eldar6776/RelayExpander/fw/DE-260124/Core/Src/modbus.c

/**
 ******************************************************************************
 * Project          : RELAY EXPANDER
 ******************************************************************************
 *
 *
 ******************************************************************************
 */

#if (__MODBUS_H__ != FW_BUILD)
    #error "modbus header version mismatch"
#endif 
/* Includes ------------------------------------------------------------------*/
#include "modbus.h"
#include <string.h>
/* Imported Types  -----------------------------------------------------------*/
/* Imported Variables --------------------------------------------------------*/
/* Imported Functions    -----------------------------------------------------*/
/* Private Typedef -----------------------------------------------------------*/
/* Private Define  -----------------------------------------------------------*/
#define COIL_ON     0x01
#define COIL_OFF    0x02
#define COIL_TOGGLE 0x03
#define COIL_READ   0x03
#define COIL_WRITE  0x06
//
/* Private Variables  --------------------------------------------------------*/
static uint8_t rec_buf[256], send_buf[32], rel[4];
static uint8_t  recb, recl, coil_max = 16, addr = 0;
/* Private macros   ----------------------------------------------------------*/
/* Private Function Prototypes -----------------------------------------------*/
static uint8_t chk_crc(uint8_t *buf);
static void mb_send(uint8_t *sb, uint8_t len);
static uint32_t getCRC16_Modbus(const uint8_t *nData, uint32_t wLength);
/* Program Code  -------------------------------------------------------------*/
/**
  * @brief
  * @param
  * @retval
  */
void mb_init(void)
{
    memset(rec_buf,0, sizeof(rec_buf));
    memset(rec_buf, 0, sizeof(rec_buf));
    memset(send_buf, 0, sizeof(send_buf));
    HAL_UART_Receive_IT(&huart1, &recb, 1);
    if(HAL_GPIO_ReadPin(SELECT_0_GPIO_Port, SELECT_0_Pin) == GPIO_PIN_RESET) addr |= 0x01U;
    if(HAL_GPIO_ReadPin(SELECT_1_GPIO_Port, SELECT_1_Pin) == GPIO_PIN_RESET) addr |= 0x02U;
    if(HAL_GPIO_ReadPin(SELECT_2_GPIO_Port, SELECT_2_Pin) == GPIO_PIN_RESET) addr |= 0x04U;
    if(HAL_GPIO_ReadPin(SELECT_3_GPIO_Port, SELECT_3_Pin) == GPIO_PIN_RESET) addr |= 0x08U;
    if(HAL_GPIO_ReadPin(SELECT_4_GPIO_Port, SELECT_4_Pin) == GPIO_PIN_RESET) addr |= 0x10U;
    if(HAL_GPIO_ReadPin(SELECT_16_32_GPIO_Port, SELECT_16_32_Pin) == GPIO_PIN_RESET) coil_max = 32;
}

void mb_service(void)
{
        uint8_t i;
    if(recl >= 8)
    {   
        i = 0;
        while(i < recl)
        {
            if(rec_buf[i] == addr)
            {
                if(rec_buf[i+1] == COIL_READ)
                {
                    if(rec_buf[i+3] < coil_max)
                    {
                        if(chk_crc(&rec_buf[i]))
                        {
                            
                        }
                    }
                }
                else if (rec_buf[i+1] == COIL_WRITE)
                {
                    if(rec_buf[i+3] < coil_max)
                    {
                        if(chk_crc(&rec_buf[i]))
                        {
                            if(rec_buf[i+4] == COIL_ON)
                            {
                                
                            }
                            else if(rec_buf[i+4] == COIL_OFF)
                            {
                                
                            }
                            else if(rec_buf[i+4] == COIL_TOGGLE)
                            {
                                
                            }
                        }
                    }
                }
            }            
            i++;
        }
    }
}


static void mb_send(uint8_t *sb, uint8_t len)
{
    HAL_UART_Transmit(&huart1,(uint8_t*)sb, len, RESP_TOUT);
    HAL_UART_Receive_IT(&huart1, &recb, 1);
}


static uint8_t chk_crc(uint8_t *buf)
{
    uint8_t crc[2];
    *((uint16_t*)crc) = getCRC16_Modbus(buf, 6);
    if((buf[6] == crc[0])&&(buf[7] == crc[1])) return 1;
    return 0;
}

static uint32_t getCRC16_Modbus(const uint8_t *nData, uint32_t wLength)
{
    static const uint32_t wCRCTable[] = 
    {
        0X0000, 0XC0C1, 0XC181, 0X0140, 0XC301, 0X03C0, 0X0280, 0XC241,
        0XC601, 0X06C0, 0X0780, 0XC741, 0X0500, 0XC5C1, 0XC481, 0X0440,
        0XCC01, 0X0CC0, 0X0D80, 0XCD41, 0X0F00, 0XCFC1, 0XCE81, 0X0E40,
        0X0A00, 0XCAC1, 0XCB81, 0X0B40, 0XC901, 0X09C0, 0X0880, 0XC841,
        0XD801, 0X18C0, 0X1980, 0XD941, 0X1B00, 0XDBC1, 0XDA81, 0X1A40,
        0X1E00, 0XDEC1, 0XDF81, 0X1F40, 0XDD01, 0X1DC0, 0X1C80, 0XDC41,
        0X1400, 0XD4C1, 0XD581, 0X1540, 0XD701, 0X17C0, 0X1680, 0XD641,
        0XD201, 0X12C0, 0X1380, 0XD341, 0X1100, 0XD1C1, 0XD081, 0X1040,
        0XF001, 0X30C0, 0X3180, 0XF141, 0X3300, 0XF3C1, 0XF281, 0X3240,
        0X3600, 0XF6C1, 0XF781, 0X3740, 0XF501, 0X35C0, 0X3480, 0XF441,
        0X3C00, 0XFCC1, 0XFD81, 0X3D40, 0XFF01, 0X3FC0, 0X3E80, 0XFE41,
        0XFA01, 0X3AC0, 0X3B80, 0XFB41, 0X3900, 0XF9C1, 0XF881, 0X3840,
        0X2800, 0XE8C1, 0XE981, 0X2940, 0XEB01, 0X2BC0, 0X2A80, 0XEA41,
        0XEE01, 0X2EC0, 0X2F80, 0XEF41, 0X2D00, 0XEDC1, 0XEC81, 0X2C40,
        0XE401, 0X24C0, 0X2580, 0XE541, 0X2700, 0XE7C1, 0XE681, 0X2640,
        0X2200, 0XE2C1, 0XE381, 0X2340, 0XE101, 0X21C0, 0X2080, 0XE041,
        0XA001, 0X60C0, 0X6180, 0XA141, 0X6300, 0XA3C1, 0XA281, 0X6240,
        0X6600, 0XA6C1, 0XA781, 0X6740, 0XA501, 0X65C0, 0X6480, 0XA441,
        0X6C00, 0XACC1, 0XAD81, 0X6D40, 0XAF01, 0X6FC0, 0X6E80, 0XAE41,
        0XAA01, 0X6AC0, 0X6B80, 0XAB41, 0X6900, 0XA9C1, 0XA881, 0X6840,
        0X7800, 0XB8C1, 0XB981, 0X7940, 0XBB01, 0X7BC0, 0X7A80, 0XBA41,
        0XBE01, 0X7EC0, 0X7F80, 0XBF41, 0X7D00, 0XBDC1, 0XBC81, 0X7C40,
        0XB401, 0X74C0, 0X7580, 0XB541, 0X7700, 0XB7C1, 0XB681, 0X7640,
        0X7200, 0XB2C1, 0XB381, 0X7340, 0XB101, 0X71C0, 0X7080, 0XB041,
        0X5000, 0X90C1, 0X9181, 0X5140, 0X9301, 0X53C0, 0X5280, 0X9241,
        0X9601, 0X56C0, 0X5780, 0X9741, 0X5500, 0X95C1, 0X9481, 0X5440,
        0X9C01, 0X5CC0, 0X5D80, 0X9D41, 0X5F00, 0X9FC1, 0X9E81, 0X5E40,
        0X5A00, 0X9AC1, 0X9B81, 0X5B40, 0X9901, 0X59C0, 0X5880, 0X9841,
        0X8801, 0X48C0, 0X4980, 0X8941, 0X4B00, 0X8BC1, 0X8A81, 0X4A40,
        0X4E00, 0X8EC1, 0X8F81, 0X4F40, 0X8D01, 0X4DC0, 0X4C80, 0X8C41,
        0X4400, 0X84C1, 0X8581, 0X4540, 0X8701, 0X47C0, 0X4680, 0X8641,
        0X8201, 0X42C0, 0X4380, 0X8341, 0X4100, 0X81C1, 0X8081, 0X4040 
    };

    uint8_t nTemp;
    uint32_t wCRCWord = 0xFFFF;

    while (wLength--)
    {
        nTemp = *nData++ ^ wCRCWord;
        wCRCWord >>= 8;
        wCRCWord ^= wCRCTable[nTemp];
    }
    return wCRCWord;
}

void HAL_UART_RxCpltCallback(UART_HandleTypeDef *huart){
    rec_buf[recl++] = recb;
    HAL_UART_Receive_IT(&huart1, &recb, 1);
}
/**
  * @brief
  * @param
  * @retval
  */
void HAL_UART_TxCpltCallback(UART_HandleTypeDef *huart){
}
/**
  * @brief
  * @param
  * @retval
  */
void HAL_UART_ErrorCallback(UART_HandleTypeDef *huart){
    __HAL_UART_CLEAR_PEFLAG(&huart1);
    __HAL_UART_CLEAR_FEFLAG(&huart1);
    __HAL_UART_CLEAR_NEFLAG(&huart1);
    __HAL_UART_CLEAR_IDLEFLAG(&huart1);
    __HAL_UART_CLEAR_OREFLAG(&huart1);
    HAL_UART_AbortReceive(&huart1);
	HAL_UART_Receive_IT(&huart1, &recb, 1);
}
/************************ (C) COPYRIGHT JUBERA D.O.O Sarajevo ************************/
