eldar6776/RelayExpander/fw/DE-260124/Core/Inc/modbus.h

/**
 ******************************************************************************
 * File Name          : modbus.h
 * Date               : 28/02/2024
 * Description        : modbus communication modul header
 ******************************************************************************
 *
 ******************************************************************************
 */

#ifndef __MODBUS_H__
#define __MODBUS_H__                         FW_BUILD // version
/* Includes ------------------------------------------------------------------*/
#include "main.h"
/* Exported Type  ------------------------------------------------------------*/
/* Exported Define  ----------------------------------------------------------*/
/* Exported macros     -------------------------------------------------------*/
/* Exported functions ------------------------------------------------------- */
void mb_init(void);
void mb_service(void);
#endif
/************************ (C) COPYRIGHT JUBERA D.O.O Sarajevo ************************/
